pinknoiz/SnapOnAirDUO/lcd240240b.jpg

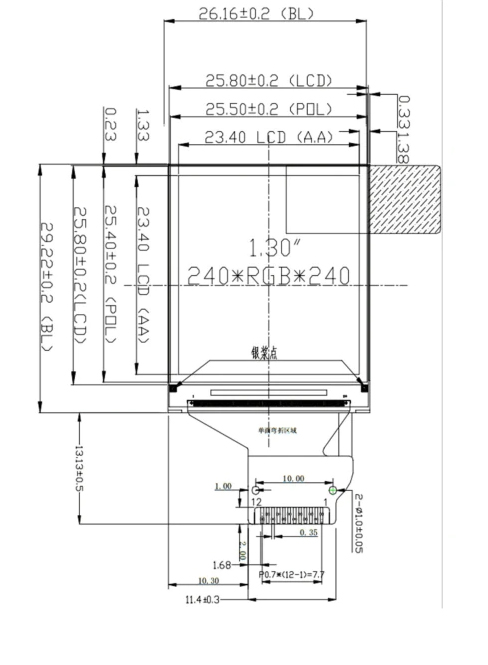
lcd240240b.jpg
