pinknoiz/SnapOnAirDUO/OLEDDisplay.jpg

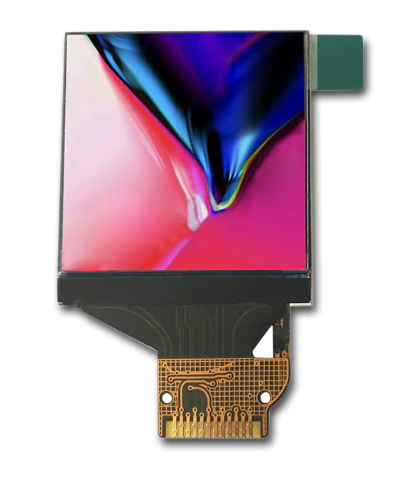
OLEDDisplay.jpg
