pinknoiz/SnapOnAirDUO/popupscreen.bmp

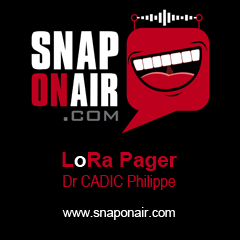
popupscreen.bmp
