pinknoiz/SnapOnAirDUO/screen.jpg

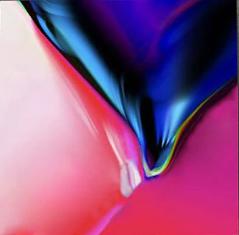
screen.jpg
