pinknoiz/SnapOnAirDUO/ttgoLoracom4.jpg

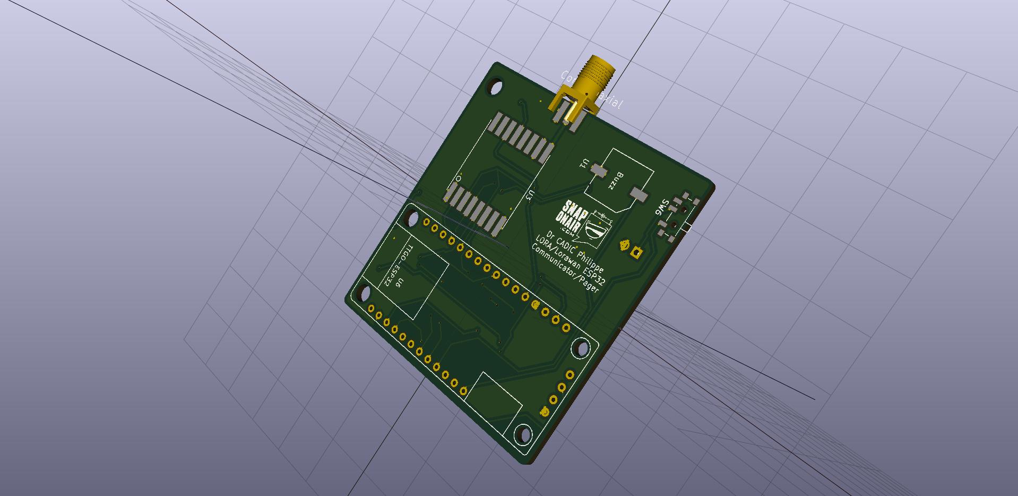
ttgoLoracom4.jpg
