pinknoiz/SnapOnAirDUO/ttgoLoracom5.jpg

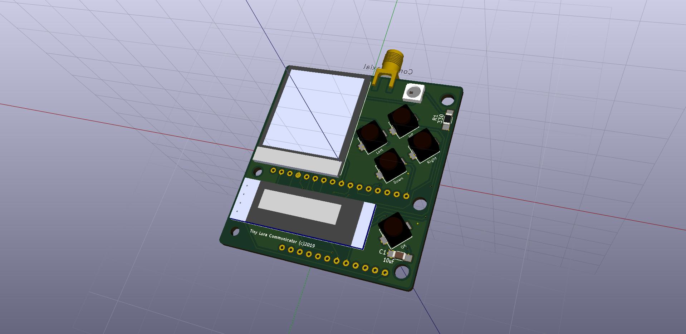
ttgoLoracom5.jpg
