pinknoiz/SnapOnAirDUO/ttgoLoracom10.jpg

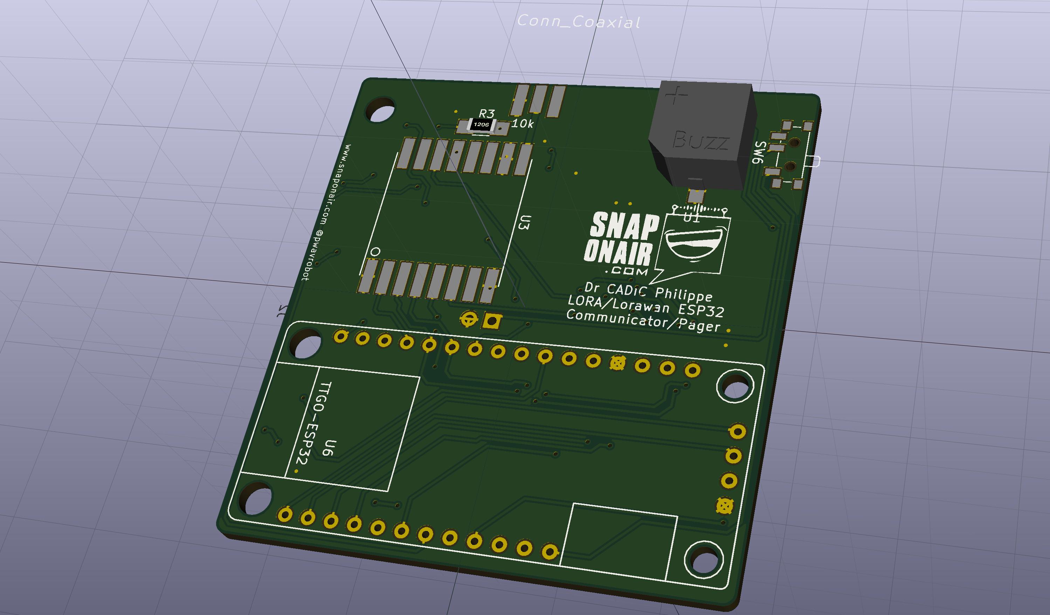
ttgoLoracom10.jpg
