pinknoiz/SnapOnAirDUO/ttgoLoracom11.jpg

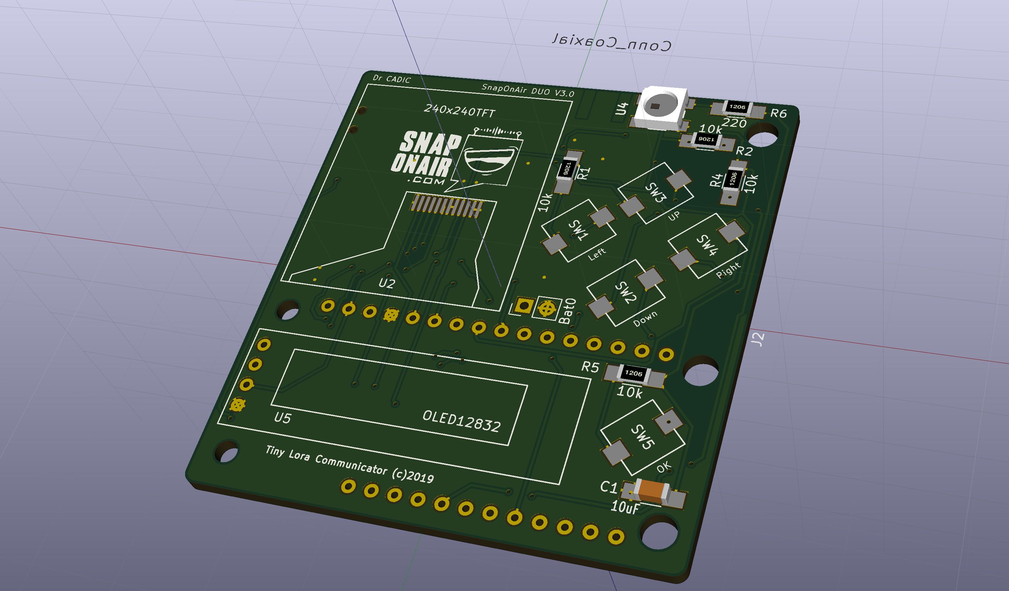
ttgoLoracom11.jpg
