pinknoiz/SnapOnAirDUO/ttgoLoracom.jpg

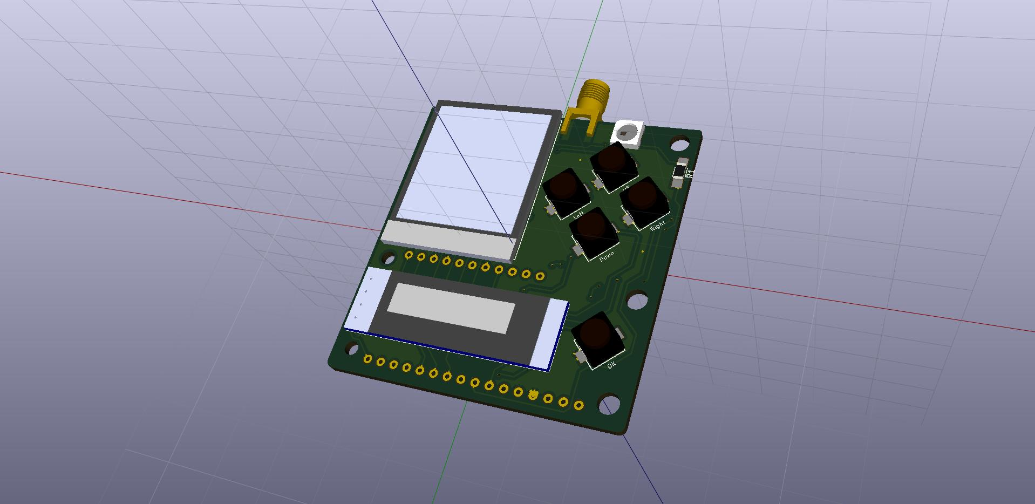
ttgoLoracom.jpg
